EAOZONE/MotionSimRepo/SOLIDWORKS/midassembly (1)/9701-24-CL.SLDPRT

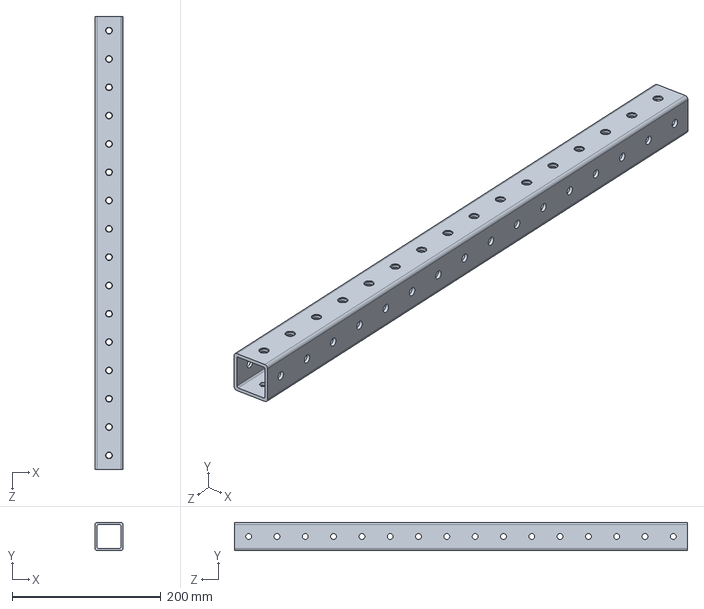
[picture p10: CAD file, 2025-10-14]
SOLIDWORKS/midassembly (1)/9701-24-CL.SLDPRT
38.1 x 38.1 x 609.6 mm
