EAOZONE/MotionSimRepo/SOLIDWORKS/midassembly (1)/mountwider.SLDPRT

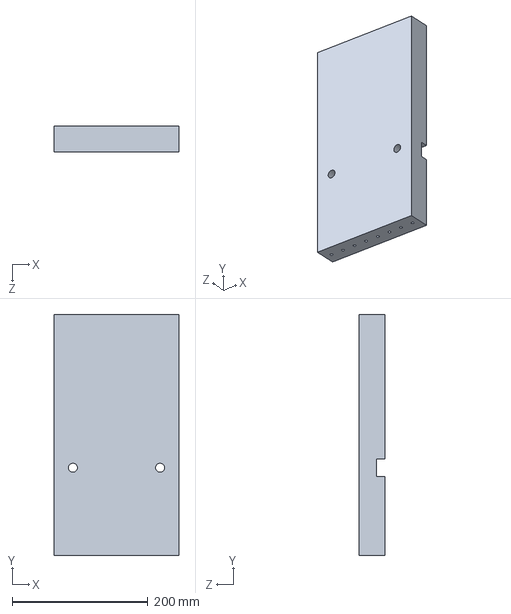
[picture p11: CAD file, 2025-10-14]
SOLIDWORKS/midassembly (1)/mountwider.SLDPRT
184.1 x 355.6 x 38.1 mm
