EAOZONE/MotionSimRepo/SOLIDWORKS/midassembly (1)/Plate.SLDPRT

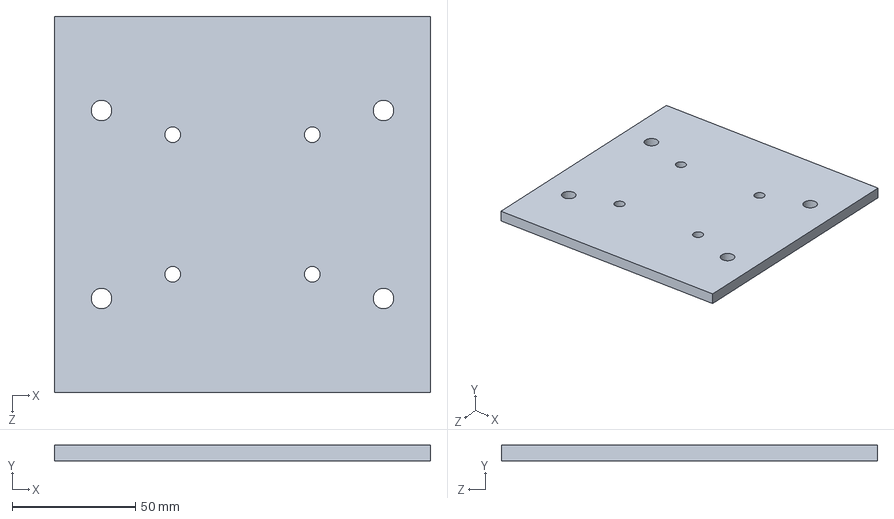
[picture p12: CAD file, 2025-10-14]
SOLIDWORKS/midassembly (1)/Plate.SLDPRT
152.4 x 6.35 x 152.4 mm
