EAOZONE/MotionSimRepo/SOLIDWORKS/midassembly (1)/Motion Simulator Wood Floor(4ftx4ft)-2023 Shorter.SLDPRT

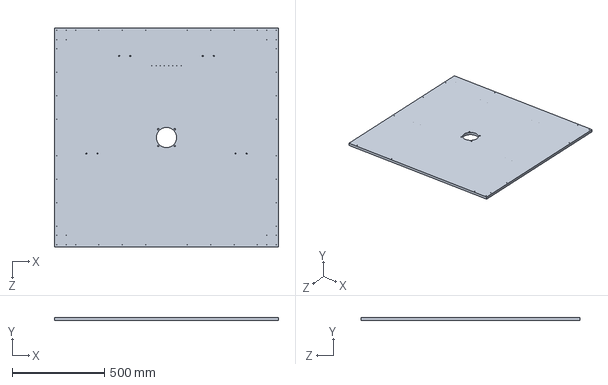
[picture p13: CAD file, 2025-10-14]
SOLIDWORKS/midassembly (1)/Motion Simulator Wood Floor(4ftx4ft)-2023 Shorter.SLDPRT
1216.0 x 17.9 x 1190.6 mm
