EAOZONE/MotionSimRepo/SOLIDWORKS/midassembly (1)/F6D250-48GU-18S_6GU50RT.SLDPRT

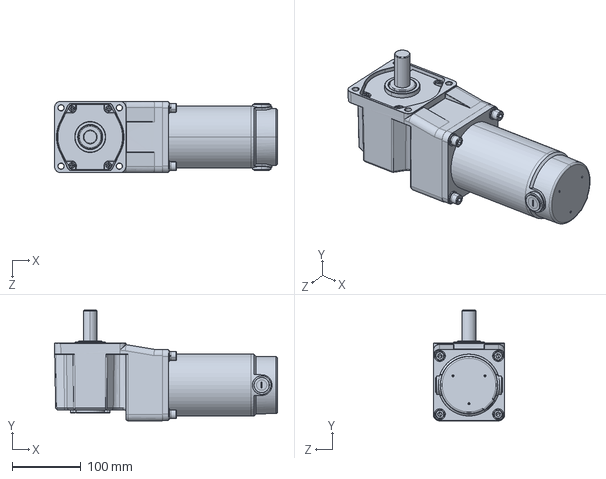
[picture p14: CAD file, 2025-10-14]
SOLIDWORKS/midassembly (1)/F6D250-48GU-18S_6GU50RT.SLDPRT
324.6 x 161.0 x 104.0 mm
