EAOZONE/MotionSimRepo/SOLIDWORKS/midassembly (1)/2by4longer.SLDPRT

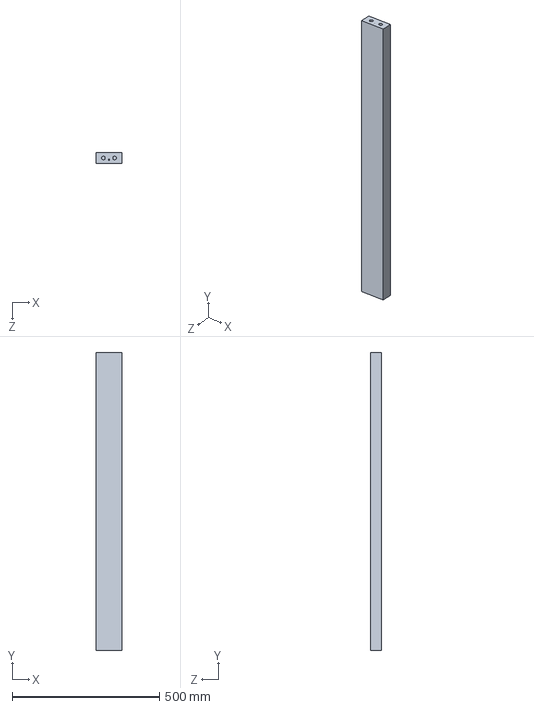
[picture p15: CAD file, 2025-10-14]
SOLIDWORKS/midassembly (1)/2by4longer.SLDPRT
88.9 x 1012.8 x 38.1 mm
