EAOZONE/MotionSimRepo/SOLIDWORKS/midassembly (1)/MotionSimulator_Seat.SLDPRT

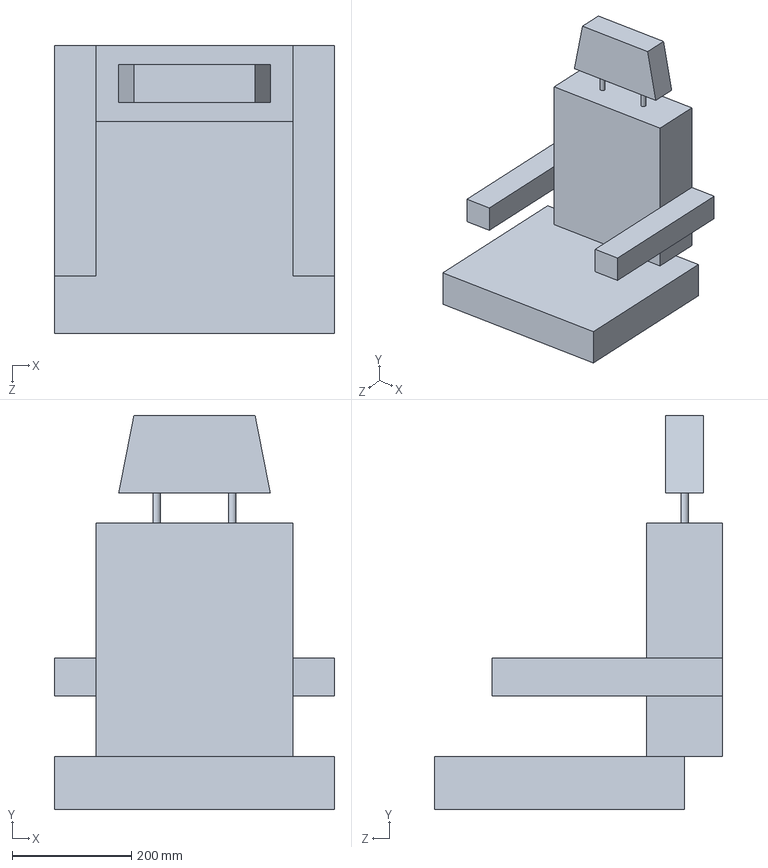
[picture p16: CAD file, 2025-10-14]
SOLIDWORKS/midassembly (1)/MotionSimulator_Seat.SLDPRT
469.9 x 660.4 x 482.6 mm
