EAOZONE/MotionSimRepo/SOLIDWORKS/midassembly (1)/EG42-G100.SLDPRT

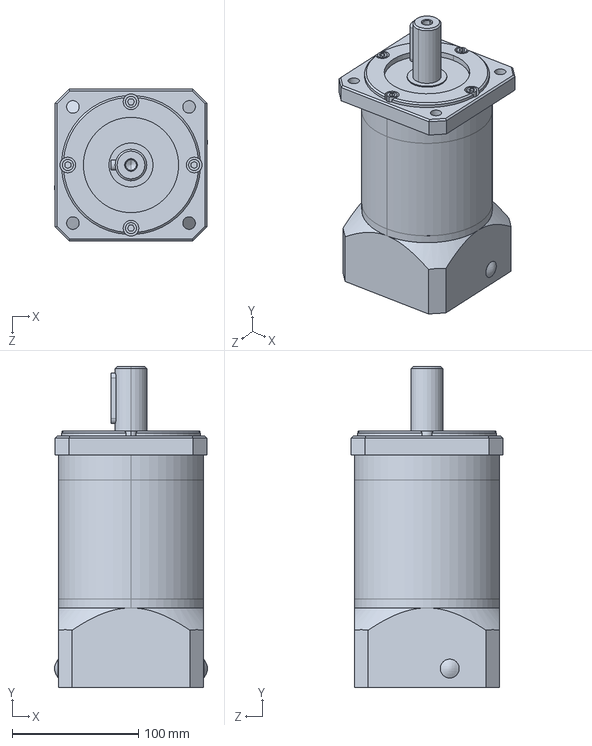
[picture p18: CAD file, 2025-10-14]
SOLIDWORKS/midassembly (1)/EG42-G100.SLDPRT
121.2 x 254.0 x 120.0 mm
