EAOZONE/MotionSimRepo/SOLIDWORKS/midassembly (1)/Cross.SLDPRT

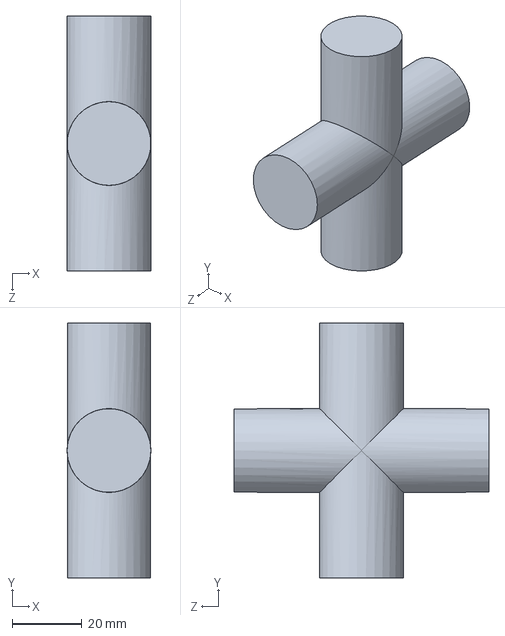
[picture p19: CAD file, 2025-10-14]
SOLIDWORKS/midassembly (1)/Cross.SLDPRT
24.0 x 73.0 x 73.0 mm
