EAOZONE/MotionSimRepo/SOLIDWORKS/midassembly (1)/9701-10_5-CL.SLDPRT

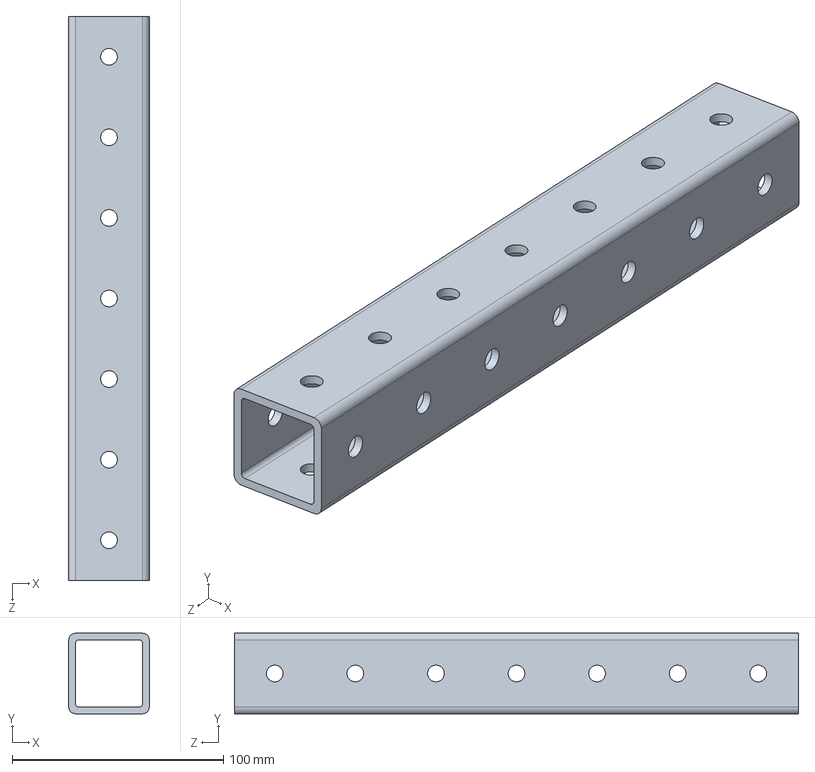
[picture p20: CAD file, 2025-10-14]
SOLIDWORKS/midassembly (1)/9701-10_5-CL.SLDPRT
38.1 x 38.1 x 266.7 mm
