EAOZONE/MotionSimRepo/SOLIDWORKS/midassembly (1)/Motor Casing.SLDPRT

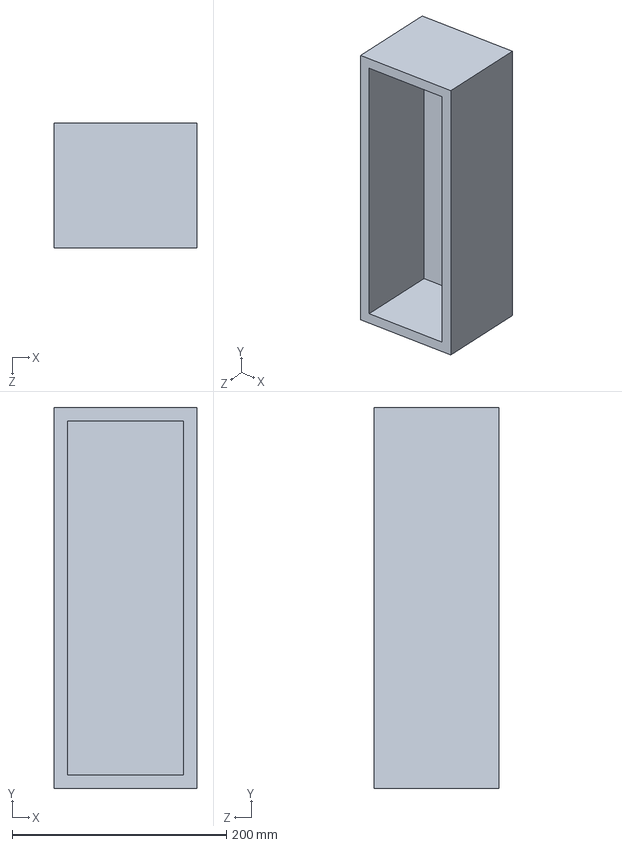
[picture p21: CAD file, 2025-10-14]
SOLIDWORKS/midassembly (1)/Motor Casing.SLDPRT
133.4 x 355.6 x 116.6 mm
