EAOZONE/MotionSimRepo/SOLIDWORKS/midassembly (1)/9701-39-CL.SLDPRT

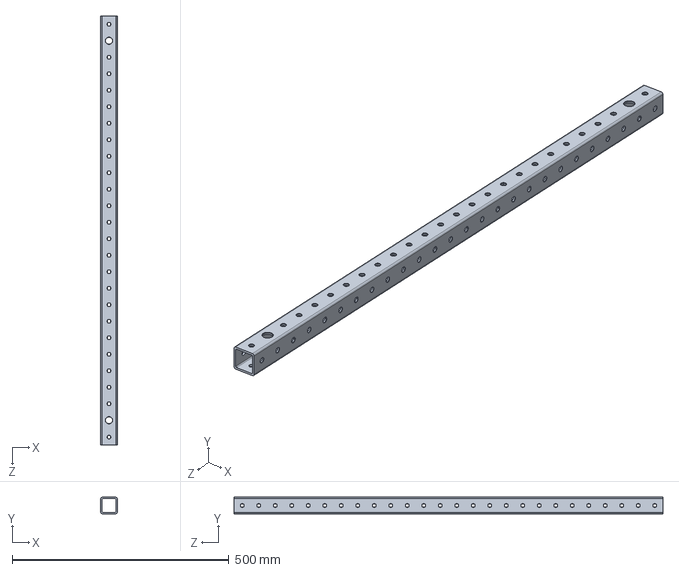
[picture p22: CAD file, 2025-10-14]
SOLIDWORKS/midassembly (1)/9701-39-CL.SLDPRT
38.1 x 38.1 x 990.6 mm
