EAOZONE/MotionSimRepo/SOLIDWORKS/midassembly (1)/9701-27-CL.SLDPRT

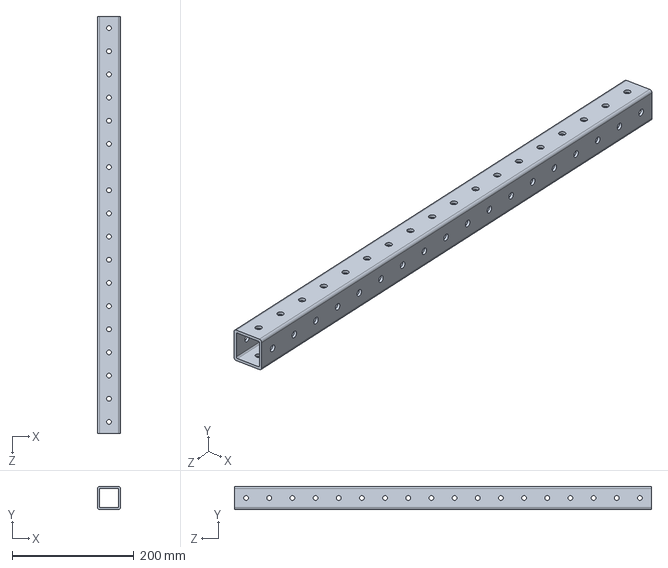
[picture p23: CAD file, 2025-10-14]
SOLIDWORKS/midassembly (1)/9701-27-CL.SLDPRT
38.1 x 38.1 x 685.8 mm
