EAOZONE/MotionSimRepo/SOLIDWORKS/midassembly (1)/Flange.SLDPRT

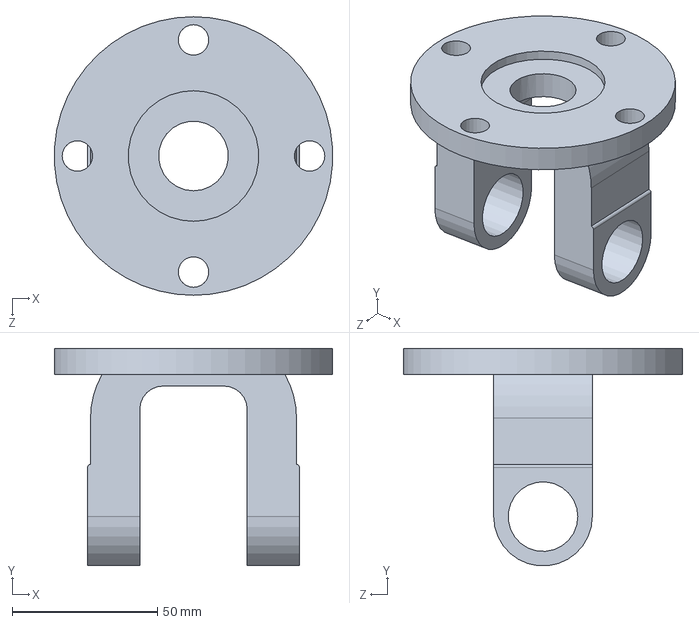
[picture p24: CAD file, 2025-10-14]
SOLIDWORKS/midassembly (1)/Flange.SLDPRT
95.8 x 74.9 x 96.0 mm
